b00lduck/stm32f4-matrixclock/src/tlc5940/driver.c

#include "main.h"
#include "driver.h"
#include "data_dma.h"
#include "tim_gsclk.h"
#include "tim_master.h"
#include "videoram.h"

void tlc5940_init(void) {
	tim_gsclk_init();
	tim_master_init();
	data_dma_init();
}
