b00lduck/stm32f4-matrixclock/src/tlc5940/tim_gsclk.c

#include "tim_gsclk.h"
#include "stm32f4xx.h"
#include "stm32f4xx_gpio.h"
#include "stm32f4xx_tim.h"
#include "stm32f4xx_rcc.h"
#include "timing.h"

void tim_gsclk_init(void) {

	// TIM1 clock enable
	RCC_APB2PeriphClockCmd(SIG_GSCLK_TIMER_CLK, ENABLE);

	// GPIO clock enable
	RCC_AHB1PeriphClockCmd(SIG_GSCLK_PORT_CLK, ENABLE);

	// GPIO configuration
	GPIO_InitTypeDef GPIO_InitStructure;
	GPIO_InitStructure.GPIO_Pin = GPIO_Pin_8;
	GPIO_InitStructure.GPIO_Mode = GPIO_Mode_AF;
	GPIO_InitStructure.GPIO_Speed = GPIO_Speed_2MHz;
	GPIO_InitStructure.GPIO_OType = GPIO_OType_PP;
	GPIO_InitStructure.GPIO_PuPd = GPIO_PuPd_NOPULL ;
	GPIO_Init(SIG_GSCLK_PORT, &GPIO_InitStructure);

	// Connect PIN8 of PORT A to alternate function (TIM1)
	GPIO_PinAFConfig(SIG_GSCLK_PORT, SIG_GSCLK_PINSOURCE, SIG_GSCLK_PIN_AF);


	// Configure the timer
	// Generate GSCLK signals

	TIM_TimeBaseInitTypeDef TIM_TimeBaseStructure;
	TIM_OCInitTypeDef  TIM_OCInitStructure;

	// Time base configuration
	TIM_TimeBaseStructure.TIM_Prescaler = CLOCK_PRESCALE;
	TIM_TimeBaseStructure.TIM_Period = 0x0003;
	TIM_TimeBaseStructure.TIM_ClockDivision = TIM_CKD_DIV2;
	TIM_TimeBaseStructure.TIM_CounterMode = TIM_CounterMode_Up;
	TIM_TimeBaseInit(SIG_GSCLK_TIMER, &TIM_TimeBaseStructure);

	// PWM1 Mode configuration: Channel1
	TIM_OCInitStructure.TIM_OCMode = TIM_OCMode_PWM2;
	TIM_OCInitStructure.TIM_OutputState = TIM_OutputState_Enable;
	TIM_OCInitStructure.TIM_Pulse = 0x0002;
	TIM_OCInitStructure.TIM_OCPolarity = TIM_OCPolarity_High;
	TIM_OC1Init(SIG_GSCLK_TIMER, &TIM_OCInitStructure);

	// Be a slave of SIG_BLANK_TIMER
	TIM_SelectInputTrigger(SIG_GSCLK_TIMER, TIM_TS_ITR2);
	TIM_SelectSlaveMode(SIG_GSCLK_TIMER, TIM_SlaveMode_Gated);
	TIM_SelectMasterSlaveMode(SIG_GSCLK_TIMER, TIM_MasterSlaveMode_Enable);

	// enable the counter
	TIM_Cmd(SIG_GSCLK_TIMER, ENABLE);

	// Main Output Enable
	TIM_CtrlPWMOutputs(SIG_GSCLK_TIMER, ENABLE);
}
